FantomZap/SN-64/docs/design/mechanical-architecture.md

# Mechanical architecture: board arrangement, insertion depths and region-free opening

Status 2026-09-29: **two-board split implemented in the schematics (evening); no PCB layout yet.** Nothing here has been fit-tested. Dimensions carry their sources; anything without a source is listed as missing, not estimated.

## Requirements this has to meet (SN_64_Engineering_Specification_Rev_A.docx)

- "Universal top opening suitable for SNES and Super Famicom cartridge shells": no region tabs; the opening accepts the North American shell and the PAL/Super Famicom shell. (The electronic lockout, the CIC, is already handled by `sn64_snes_cic_lock`, which answers either region's key.)
- "High-cycle cartridge connector and mechanically keyed insertion": a cartridge cannot go in reversed.
- "Physical validation against the M64 cartridge bay and eject mechanism."
- Layout guidance: SNES translators close to the top connector, N64 interface close to the bottom edge, FPGA centrally between them.
- Mechanical abuse tests: insertion force, wobble, repeated cycles, accidental side loading.

## The orientation problem

The SN64 stands upright in the N64/M64 slot, and the SNES cartridge enters from the top, parallel to it. A standard SNES console socket is a vertical through-hole part: its contacts face away from the board it is soldered to, so on an upright board the cartridge would stick out sideways.

A single-board design would need a **right-angle** 62-contact card-edge socket at the SNES's **2.5 mm** pitch. None was found: the only right-angle 62-position edge slot in the LCSC/JLC catalogue (WingTAT ER62BGFBK, LCSC C5173349) is **2.54 mm** pitch, which accumulates 30 × 0.04 = 1.2 mm of error across a row and cannot mate reliably with a 2.5 mm cartridge edge. The Super Game Boy solves the same problem for Game Boy carts with a right-angle connector (reused by MouseBiteLabs' open [Super Game Boy Plus](https://github.com/MouseBiteLabs/Super-Game-Boy-Plus)), but no SNES equivalent is sourced.

## Decision: two rigid boards (implemented)

- **Main board (upright):** N64 edge (SummerCart64 geometry), FPGA, power, USB-C, clocks, audio ADC.
- **Socket board (horizontal, on top):** a standard vertical SNES socket (candidate NES Repair Shop `snspt043`, see [socket-selection.md](socket-selection.md)), plus the 5 V/3.3 V translators the spec wants close to the socket.
- **Joint:** a 2x40 2.00 mm pin header pair (right-angle on the main board's top edge, vertical socket on the socket board), carrying the raw 5 V cartridge signals: joint pins 1-62 = socket contacts 1-62 (same names), 63-66 = cartridge 5 V, 67-80 = GND. The translators stay on the main board's top edge, within a few centimetres of the socket, which meets the spec's "close to the top connector". Implemented by `hardware/sn64/tools/split_socket_board.py`: the main root's J2 is now the joint header; `hardware/sn64-socket/` is the socket board project (J1 socket on `SN64:SNES_Slot_Console_7mm`, J2 joint socket, two 100 nF on the 5 V). `tools/verify_socket_joint.py` checks the two netlists pin by pin (9/9, negative 3/3). Open: signal integrity of the 80 mm header at SNES bus edge rates (ground-pin interleave if measurements demand it); the joint must not carry cartridge insertion loads (shell support).

Advantages: standard, replaceable socket; the cartridge load goes into a horizontal board that the shell can support directly, instead of into the N64 slot through the main board. Costs: a second board and a connector.

Alternatives kept open: rigid-flex (costly), or a right-angle 2.5 mm socket if a real one is found.

## Depths and clearances

| Interface | Known (source) | Missing |
|---|---|---|
| SN64 into N64/M64 | Edge contacts 2.5 mm pitch, 60.0 mm span; tongue shoulder to insertion tip 10.5 mm; PCB 1.2 mm ([dimensions.md](../dimensions.md), SummerCart64 `a1e7996d`). SummerCart64 shell envelope about 116.1 × 89.4 × 18.1 mm; SummerCart64 is confirmed to work in the M64. **Decision (owner, 2026-09-29): a cartridge that fits an N64 fits an M64; the SN64 lower body follows the SummerCart64 shell and no further M64 CAD work is done before a prototype.** | The spec's physical validation against the M64 bay and eject mechanism, on a real unit, once a prototype exists. (ModRetro's Parasolid cart-body/door CAD stays on file if ever needed.) |
| SNES cartridge into SN64 | Socket pin pattern: 62 contacts, 2.5 mm pitch; rows 5.0 mm (Sanni cart-reader socket) or 7.0 mm (OpenSFC original console socket, body 99.0 × 11.25 mm, Ø3.2 mm ears 95.0 mm apart). Cartridge fingers occupy the bottom 1–8 mm of the edge (sd2snes Rev F). See [dimensions.md](../dimensions.md). | Socket height above board and contact position (sample); which socket family the sample is. |
| Cartridge shells | Super Famicom shell CAD (SNESDRONE, usagi_ CC-BY-3.0); published outer sizes NA 136 × 88 × 20 mm, SFC/PAL 130 × 86 × 20 mm (Wikipedia; see [dimensions.md](../dimensions.md)). | Measured bottom-edge profiles of a NA and an SFC/PAL shell, and the flashcart shells (Super EverDrive X5/X6, FXPAK Pro). |

"Safely inside" means: the edge fully engaged in the socket, the shell resting on the SN64's top rim (as on a console) so a tall cartridge cannot lever against the N64 slot, and keying that stops reversed insertion for every shell style.

## Next steps

1. Gather the missing dimensions above: downloadable CAD first (ModRetro M64, SNES shell models), then measurements of real parts where no drawing exists.
2. Fix the two-board split and the joint connector.
3. Only then draw the board outlines and start placement.
