FantomZap/SN-64/SN_64_Engineering_Specification_Rev_A.docx

SN 64
FPGA SNES Cartridge Adapter for Nintendo 64 and ModRetro M64

Engineering Specification • Revision A • September 2026

# 1. Product Definition

SN 64 is a modern FPGA-based successor in concept to the TriStar 64's SNES functionality. It recreates the console-side SNES environment required by real cartridges while using an original Nintendo 64 or ModRetro M64 as the host/controller platform.

The top slot is required to behave electrically and temporally like a genuine SNES/Super Famicom cartridge interface. Original cartridges, Super EverDrive X5/X6 and FXPAK Pro are first-class targets.

# 2. Hard Requirements

- Original Nintendo 64 operation with no internal console modification.
- ModRetro M64 operation using ordinary N64-cartridge-compatible behavior.
- Original SNES/SFC cartridge support.
- Explicit Super EverDrive X5/X6 and FXPAK Pro validation.
- Complete 62-pin SNES interface including expansion pads and cartridge audio inputs.
- FPGA-based SNES motherboard logic and timing-sensitive N64 interface.
- Electrical protection for host, adapter and cartridge.
- Field-updatable FPGA/firmware with independent recovery programming.
- Manufacturing test pads, telemetry and diagnostic firmware.

# 3. Architecture

N64 / M64 → N64 cartridge-bus interface → FPGA + protection/support logic → SNES motherboard core → protected 5 V SNES cartridge interface → SNES/SFC cartridge, Super EverDrive or FXPAK Pro.

The original TriStar proves the concept but is not copied circuit-for-circuit. Its obsolete NES subsystem, cheat hardware, memory editor and analog switching are omitted.

# 4. SNES Cartridge Interface

The 62-contact SNES connector carries A0–A23, D0–D7, /RD, /WR, /ROMSEL, /IRQ, /RESET, SYSTEM CLK, PHI2, PA0–PA7, /PRD, /PWR, /WRAMSEL, REFRESH, EXPAND, CIC-related lines, +5 V, grounds, enhancement/expansion pads and left/right cartridge audio inputs.

The cartridge domain is 5 V. FPGA pins must not rely on undocumented 5 V tolerance. Proper direction-controlled translation/buffering is required, including power-off isolation and contention-safe bidirectional data handling.

Cartridge +5 V uses a protected high-side load switch with soft start, current limiting, reverse-current blocking, voltage/current sensing and a hardware default-OFF state until configuration and rail checks pass.

# 5. FPGA SNES Subsystem

The FPGA reproduces the console-side CPU, PPU, APU, memory map, DMA/HDMA, timers, arbitration and cartridge timing. With a physical cartridge inserted, cartridge ROM and cartridge-specific hardware remain outside the FPGA.

A mature open SNES FPGA core can be adapted, but its ROM-loader path must be replaced by a physical cartridge bridge.

SNES WRAM and other cycle-critical memories require deterministic latency. BRAM is preferred where practical, with synchronous external RAM only where timing is characterized.

A low-jitter oscillator and FPGA clock management generate SNES timing. NTSC is the first validation target; PAL remains an architectural target. Cartridge clock outputs include tunable series termination footprints.

# 6. N64 and M64 Host Interface

The lower edge presents SN 64 as an N64 cartridge. FPGA logic implements the timing-sensitive cartridge endpoint plus a mailbox/register protocol for a small N64-side bootstrap.

The host reads N64 controller state, presents configuration/diagnostics and forwards controller data to the SNES subsystem.

Controller mapping is firmware-configurable. Default mapping uses the D-pad directly, maps N64 face/C/shoulder buttons to SNES A/B/X/Y/L/R, Start to Start and Z to Select.

Baseline M64 support must depend only on behavior available to an ordinary N64 cartridge. A future enhanced M64 path is reserved until ModRetro's public console implementation exposes a supported integration mechanism.

# 7. Video and Audio

Rev A provides an independent digital SNES video/audio output for validation. This avoids assuming that full SNES A/V can be transported through the original N64 cartridge interface.

The original TriStar generated its own A/V and switched analog video. SN 64 does not need to retain that legacy topology.

The long-term M64 target is single-HDMI operation through the M64. PCB and FPGA resources are reserved for that path, but no undocumented M64 interface is invented.

# 8. Safety and Protection

- Input overcurrent protection and reverse-current protection where applicable.
- Protected switched cartridge +5 V.
- Supervised FPGA core and I/O rails.
- ESD protection on externally accessible connectors.
- Power-off isolation on translators.
- Controlled reset and power sequencing.
- Series termination footprints on clocks and sensitive buses.
- Bulk and local high-frequency decoupling.
- Grounding that keeps noisy digital returns away from sensitive A/V references.
- Board temperature monitoring.
- Safe FPGA default state with external bus outputs high impedance until configuration succeeds.

SNES cartridges are not treated as hot-swappable. Firmware should require cartridge power-down before insertion/removal. Protection mitigates mistakes but does not redefine the connector as a hot-plug standard.

Host-readable telemetry should include cartridge voltage/current, FPGA rails, input voltage, temperature, configuration state, overcurrent history and reset reason.

# 9. Firmware and Recovery

FPGA image blocks: N64 endpoint, SNES core, physical cartridge bridge, controller mailbox, power-control state machine, A/V pipeline, telemetry registers and watchdog/fail-safe logic.

The N64 bootstrap initializes the adapter, verifies health, reads controllers, exposes configuration and diagnostics, and refuses to enable cartridge power on a reported fault.

Recovery programming must work without a successful N64 boot. JTAG or a dedicated service interface is mandatory.

Production-oriented updates should use versioned images, integrity checking and a known-good recovery strategy.

# 10. Mechanical Design

- N64-compatible lower edge geometry.
- Universal top opening suitable for SNES and Super Famicom cartridge shells.
- High-cycle cartridge connector and mechanically keyed insertion.
- Structural support so a tall SNES cartridge cannot lever against the N64/M64 connector.
- Service/programming access.
- Thermal copper/ventilation sized from measured dissipation.
- Physical validation against the M64 cartridge bay and eject mechanism.

# 11. PCB Architecture

A multilayer PCB is required. Four layers may be possible, but six layers are preferred if routing density, return paths and A/V integrity justify it.

SNES translators should sit close to the top connector, N64 interface circuitry close to the bottom edge, FPGA centrally between the two domains, clock close to FPGA, regulators with short current loops, and A/V circuitry separated from switching noise.

Manufacturing test pads should be concentrated on one side where possible for a bed-of-nails fixture.

# 12. Manufacturing Package

- KiCad schematic and PCB source.
- PDF schematic set.
- Gerbers and NC drill files.
- Stack-up and fabrication notes.
- BOM with manufacturer part numbers and approved alternates.
- PCBWay assembly BOM and CPL/pick-and-place.
- Assembly drawings.
- Programming and initial-power-up procedure.
- Test-point map and JTAG notes.
- Mechanical STEP model and enclosure interface dimensions.

# 13. Bring-Up Procedure

1. Inspect the unpowered board and check for shorts.
2. Power from a current-limited bench supply with no console and no SNES cartridge.
3. Validate every rail, sequence and quiescent current.
4. Program a minimal FPGA image that leaves external buses high impedance.
5. Validate N64-side idle levels using a test fixture before valuable hardware.
6. Validate switched cartridge +5 V using a dummy electronic load.
7. Measure SNES clocks, amplitudes, ringing and edge rates.
8. Exercise address/data/control buses using a passive test cartridge or logic-analyzer fixture.
9. Boot the N64 diagnostic ROM and validate mailbox/controller communication.
10. Test a simple original SNES cartridge.
11. Test SRAM-bearing cartridges.
12. Test Super EverDrive.
13. Test FXPAK Pro.
14. Test enhancement-chip cartridges and FXPAK enhancement implementations.
15. Repeat on M64 and compare behavior.
16. Run fault-injection tests before extended compatibility testing.

# 14. Compatibility Certification

Each target gets recorded results for cold boot, warm reset, controls, video, audio, saves, cartridge reset behavior and extended runtime.

Matrix targets include LoROM, HiROM, battery SRAM, DSP, Super FX, SA-1, S-DD1, Cx4, Super EverDrive X5/X6, FXPAK Pro ordinary ROMs, FXPAK Pro enhancement implementations, representative N64 revisions, PAL where available, M64 stock timing and M64 overclock modes as a separate non-baseline category.

# 15. Additional Requirements Worth Adding

Licensing: keep third-party HDL license obligations explicit. If GPL-licensed core code is distributed in SN 64 firmware, corresponding source and license requirements must be honored.

Component lifecycle: choose FPGA, regulators, translators and memory with good availability and define drop-in alternates where possible.

Firmware identity: expose hardware revision, FPGA build ID and firmware version in diagnostics so compatibility reports are reproducible.

Factory test mode: include a self-test image capable of checking RAM, buses, clock outputs, cartridge power telemetry and host communication without a game cartridge.

Golden test cartridge: design a small passive/active diagnostic cartridge for production and repair. It can loop bus signals, provide known ROM/SRAM behavior and expose measurement points.

Boundary protection: include footprints for optional damping/pull components so Rev A signal-integrity discoveries can be tuned without a PCB respin.

Thermal margin: validate worst-case cartridge load and FPGA utilization in an enclosure, not only on an open bench.

Brownout behavior: explicitly test console power cycling, brief input droops and interrupted FPGA configuration.

Save integrity: test that power-down/reset cannot corrupt cartridge SRAM or flashcart state.

EMI/EMC pre-compliance: even for a hobby prototype, measure obvious radiated/conducted problems before considering a production run.

Mechanical abuse: test cartridge insertion force, wobble, repeated cycles and accidental side loading.

Legal branding: SN 64 should avoid implying Nintendo, ModRetro or Krikzz endorsement unless permission exists.

# 16. Rev A Success Criteria

Rev A succeeds when it boots safely on both an original N64 and M64, accepts a representative set of original SNES cartridges, operates Super EverDrive and FXPAK Pro reliably, preserves saves, produces stable A/V, survives reset/power-cycle testing, reports electrical faults correctly and can recover from a deliberately invalid firmware image without hardware rework.

Only after those criteria are met should the design be reduced in cost, miniaturized or treated as a production candidate.

# 17. Known Unknowns Before Fabrication

Exact FPGA selection and package after synthesis of the chosen SNES core plus physical cartridge bridge.

Exact translator family after propagation-delay and direction-control analysis.

Exact external-memory requirement after synthesis/timing closure.

Final Rev A digital A/V transmitter/interface.

Measured current envelope for original cartridges, Super EverDrive and FXPAK Pro.

Mechanical dimensions from physical N64/M64 fit checks.

Future M64 enhanced digital A/V/control interface pending public implementation details.

# 18. Source Notes

TriStar 64 FAQ and setup/behavior documentation: GameFAQs, MercilessDeth, 'Nintendo 64 - Tristar 64 FAQ.'

SNES cartridge connector and signal descriptions: SNESdev Wiki, 'Cartridge connector.'

SNES connector cross-reference: AllPinouts, 'SNES Cartridge.'

SNES FPGA behavior/reference: MiSTer FPGA Documentation, 'SNES,' and SNES_MiSTer project.

M64 architecture and open-source intent: ModRetro M64 product page and 'FPGA Development Deep Dive.'

Current public M64 repository status: ModRetro GitHub organization, oss-m64-console.

N64 FPGA cartridge precedent: SummerCart64 open-source project and associated hardware documentation.

Prototype design specification • September 2026

SN 64 • Engineering Specification • Rev A
