FantomZap/SN-64/hardware/sn64/tools/split_socket_board.py

"""Split the SNES socket onto its own board (two-board design, docs/design/mechanical-architecture.md).

Main project (hardware/sn64): the root's J2 becomes the socket-board joint, a 2x40 2.00 mm
right-angle pin header (SN64:SN64_Socket_Joint_2x40). Its pins 1-62 keep the socket symbol's
names and drawing positions, so the existing root wiring is untouched; pins 63-66 (SNES_5V_CART)
and 67-80 (GND) get new wires and labels.

Socket project (hardware/sn64-socket): a new KiCad project with J1 = the real socket on the
console-replacement footprint built from OpenSFC's CartSlot geometry (7.0 mm rows, ears 95 mm
apart) and J2 = the mating 2x40 2.00 mm vertical socket, wired 1:1 with the same net names as
the main root, plus two 100 nF capacitors on the cartridge 5 V.

Idempotent: refuses to run twice unless --force (which regenerates the socket project and
re-applies the root edit only if J2 is still the old socket symbol). Never rerun the root
generators; this script edits the root natively, line by line.
"""
import argparse
import hashlib
import json
import re
import uuid
from pathlib import Path

HERE = Path(__file__).resolve().parent
PROJECT = HERE.parent                       # hardware/sn64
SOCKET = PROJECT.parent / 'sn64-socket'     # hardware/sn64-socket
LIB_SYM = PROJECT / 'libraries/SN64.kicad_sym'
LIB_FP = PROJECT / 'libraries/SN64.pretty'
ROOT = PROJECT / 'sn64.kicad_sch'

JOINT = 'SN64_Socket_Joint_2x40'
JOINT_FP_MAIN = 'Connector_PinHeader_2.00mm:PinHeader_2x40_P2.00mm_Horizontal'
JOINT_FP_SOCKET = 'Connector_PinSocket_2.00mm:PinSocket_2x40_P2.00mm_Vertical'
SOCKET_FP = 'SNES_Slot_Console_7mm'
EXTRA = [(n, 'SNES_5V_CART') for n in range(63, 67)] + [(n, 'GND') for n in range(67, 81)]
# OpenSFC CartSlot.kicad_mod, commit 6574450b, SHA-256 1f9b60dd...48b5a0 (docs/dimensions.md)
OPENSFC = {'pad_size': 1.5, 'drill': 1.0, 'row_y': 3.5, 'pitch': 2.5, 'gap': 7.5, 'x0': -42.5,
           'body': (-49.5, -5.65, 49.5, 5.60), 'ear_x': 47.5, 'ear_d': 3.2}


def uid(*parts):
    return str(uuid.uuid5(uuid.NAMESPACE_URL, 'sn64-socket-split/' + '/'.join(map(str, parts))))


def pad_x(index):
    """x of contact 1..31 along a row: 2.5 mm pitch with 7.5 mm gaps after contacts 4 and 27."""
    x = OPENSFC['x0']
    for k in range(1, index):
        x += OPENSFC['gap'] if k in (4, 27) else OPENSFC['pitch']
    return round(x, 3)
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
